woytekm/QSID/os/synth/lfo.c

#include "common.h"
#include "defs.h"
#include "patch.h"
#include "lfo.h"
#include "task.h"
#include "inventory.h"

void SYNTH_LFO1(void)
 {
  int LFO1_input_pipe;
  uint8_t retrigger, waveform_changed, routing_changed, input_msg, lfo_off, current_destination, i;
  int16_t LFO_step, mod_value, apply_value, apply_value_osc1,
           apply_value_osc2, apply_value_osc3, pipe_read_delay, falling_edge, readed;
  int16_t LFO_ranges[10];
  int16_t LFO_steps[10];

  lfo_off = 1;
  mod_value = 0;
  pipe_read_delay = 0;
  falling_edge = 1;

  apply_value = apply_value_osc1 = apply_value_osc2 = apply_value_osc3 = 0;

  LFO1_input_pipe = G_QSID_tasks[TASK_LFO1].input_pipe[0];

  if (fcntl(LFO1_input_pipe, F_SETFL, O_NONBLOCK) == -1) 
   {
    SYS_debug(DEBUG_NORMAL,"SYNTH_lfo1: fcntl on input pipe failed: %d", errno);
    return;
   }

  LFO_ranges[LFO_ROUTING_CUTOFF] = CUTOFF_RANGE;
  LFO_ranges[LFO_ROUTING_PW_1] = PW_RANGE;
  LFO_ranges[LFO_ROUTING_PW_2] = PW_RANGE;
  LFO_ranges[LFO_ROUTING_PW_3] = PW_RANGE;
  LFO_ranges[LFO_ROUTING_PW_ALL] = PW_RANGE;

  LFO_ranges[LFO_ROUTING_DETUNE_1] = DETUNE_RANGE;
  LFO_ranges[LFO_ROUTING_DETUNE_2] = DETUNE_RANGE;
  LFO_ranges[LFO_ROUTING_DETUNE_3] = DETUNE_RANGE;
  LFO_ranges[LFO_ROUTING_DETUNE_ALL] = DETUNE_RANGE;

  LFO_ranges[LFO_ROUTING_MAIN_VOLUME] = VOLUME_RANGE;

  LFO_steps[LFO_ROUTING_CUTOFF] = 20;
  LFO_steps[LFO_ROUTING_PW_1] = 50;
  LFO_steps[LFO_ROUTING_PW_2] = 50;
  LFO_steps[LFO_ROUTING_PW_3] = 50;
  LFO_steps[LFO_ROUTING_PW_ALL] = 50;

  LFO_steps[LFO_ROUTING_DETUNE_1] = 1;
  LFO_steps[LFO_ROUTING_DETUNE_2] = 1;
  LFO_steps[LFO_ROUTING_DETUNE_3] = 1;
  LFO_steps[LFO_ROUTING_DETUNE_ALL] = 1;

  LFO_steps[LFO_ROUTING_MAIN_VOLUME] = 1; 

  while( 1 )
   {

     usleep(LFO_BASE_TICK + (100000/G_current_patch.LFO1_rate));
     
     pipe_read_delay++;

     if(pipe_read_delay == 5)
      {
       readed = read(LFO1_input_pipe, &input_msg, sizeof(input_msg));
       pipe_read_delay = 0;
      }

     if(readed > 0)
      {
       SYS_debug(DEBUG_HIGH,"SYNTH_LFO1: input pipe data: 0x%X (readed %d bytes)",input_msg, readed);
       if((input_msg >= 0) && (input_msg <= 14))
        {
         if(input_msg == 0)
          {
           lfo_off = 1;
           //reset register values to patch settings here!
          }
         else if(input_msg <= 10)
          {
           routing_changed = 1;
           current_destination = input_msg;
           lfo_off = 0;
          }
         else 
           waveform_changed = 1;
        }
       readed = 0;
      }

     if(lfo_off) continue;

     if((waveform_changed) || (routing_changed))
      {
       mod_value = 0;
       LFO_step = LFO_steps[current_destination];
       waveform_changed = routing_changed = 0;
      }

     switch(G_current_patch.LFO1_shape)
      {
       case LFO_SHAPE_TRIANGLE:
        mod_value += LFO_step;
        /* printf("step: %d, mod value: %d\n",LFO_step, mod_value); */
        if((mod_value >= ((G_current_patch.LFO1_depth*LFO_steps[current_destination])/2)))
           {
            falling_edge = -1;
            LFO_step = LFO_steps[current_destination] * -1;
            /* printf("mod_value reached upper range, changing step to negative %d\n",LFO_step); */
           }
        else if((mod_value <= ((G_current_patch.LFO1_depth*LFO_steps[current_destination])/2) * -1 ))
           {
            falling_edge = 1;
            LFO_step = LFO_steps[current_destination];
            /* printf("mod_value reached lower range, changing step to positive %d\n",LFO_step); */
           }
        break;

       case LFO_SHAPE_SAWTOOTH:
        mod_value += LFO_step;
        if((mod_value >= (G_current_patch.LFO1_depth*LFO_step)/2))
          mod_value = ((G_current_patch.LFO1_depth*LFO_step)/2) * -1;
        break;
      }

    /* printf("LFO mod value: %d\n",mod_value); */
    /* printf("G_current_patch.LFO1_depth * falling_edge: %d\n",G_current_patch.LFO1_depth * falling_edge); */

    switch(current_destination)
     {
        case LFO_ROUTING_CUTOFF:
        apply_value = G_current_patch.filter_cutoff + mod_value + (G_current_patch.LFO1_depth * falling_edge);

        /* clip the value if it went out of range */
        if(apply_value < 0) apply_value = 0;
        else if(apply_value > LFO_ranges[current_destination]) 
         apply_value = LFO_ranges[current_destination];

        for(i = 1; i <= G_inventory_voice_count; i++)
          LIB_SID_modulate_cutoff(G_voice_inventory[i].address, apply_value);
        break;

        case LFO_ROUTING_PW_1:
        apply_value = G_current_patch.osc1_pw + mod_value;

        if(apply_value < 0) apply_value = 0;
        else if(apply_value > LFO_ranges[current_destination]) 
         apply_value = LFO_ranges[current_destination];

        for(i = 1; i <= G_inventory_voice_count; i++)
          LIB_SID_modulate_PW1(G_voice_inventory[i].address, apply_value);
        break;

        case LFO_ROUTING_PW_2:
        apply_value = G_current_patch.osc2_pw + mod_value;

        if(apply_value < 0) apply_value = 0;
        else if(apply_value > LFO_ranges[current_destination]) 
         apply_value = LFO_ranges[current_destination];

        for(i = 1; i <= G_inventory_voice_count; i++)
          LIB_SID_modulate_PW2(G_voice_inventory[i].address ,apply_value);
        break;

        case LFO_ROUTING_PW_3:
        apply_value = G_current_patch.osc3_pw + mod_value;

        if(apply_value < 0) apply_value = 0;
        else if(apply_value > LFO_ranges[current_destination]) 
         apply_value = LFO_ranges[current_destination];

        for(i = 1; i <= G_inventory_voice_count; i++)
          LIB_SID_modulate_PW3(G_voice_inventory[i].address ,apply_value);
        break;

        case LFO_ROUTING_PW_ALL:
        apply_value_osc1 = G_current_patch.osc1_pw + mod_value;
        apply_value_osc2 = G_current_patch.osc2_pw + mod_value;
        apply_value_osc3 = G_current_patch.osc3_pw + mod_value;

        if(apply_value_osc1 < 0) apply_value_osc1 = 0;
        else if(apply_value_osc1 > LFO_ranges[current_destination]) 
         apply_value_osc1 = LFO_ranges[current_destination];

        if(apply_value_osc2 < 0) apply_value_osc2 = 0;
        else if(apply_value_osc2 > LFO_ranges[current_destination])
         apply_value_osc2 = LFO_ranges[current_destination];

        if(apply_value_osc3 < 0) apply_value_osc3 = 0;
        else if(apply_value_osc3 > LFO_ranges[current_destination])
         apply_value_osc3 = LFO_ranges[current_destination];

        for(i = 1; i <= G_inventory_voice_count; i++)
         {
          LIB_SID_modulate_PW1(G_voice_inventory[i].address ,apply_value_osc1);
          LIB_SID_modulate_PW2(G_voice_inventory[i].address ,apply_value_osc2);
          LIB_SID_modulate_PW3(G_voice_inventory[i].address ,apply_value_osc3);
         }
        break;
     }

    /* printf("LFO apply value: %d\n",apply_value); */

   }

  }
