woytekm/QSID/os/midi/sysex_handlers.h

uint8_t MIDI_SYSEX_OSC1_STATE_CBK(unsigned char *message_buffer, uint16_t buffer_len);
uint8_t MIDI_SYSEX_OSC1_FINE_CBK(unsigned char *message_buffer, uint16_t buffer_len);
uint8_t MIDI_SYSEX_OSC1_COARSE_CBK(unsigned char *message_buffer, uint16_t buffer_len);
uint8_t MIDI_SYSEX_OSC1_PW_CBK(unsigned char *message_buffer, uint16_t buffer_len);
uint8_t MIDI_SYSEX_OSC1_WAVE_CBK(unsigned char *message_buffer, uint16_t buffer_len);
uint8_t MIDI_SYSEX_OSC1_RINGMOD_CBK(unsigned char *message_buffer, uint16_t buffer_len);
uint8_t MIDI_SYSEX_OSC1_SYNC_CBK(unsigned char *message_buffer, uint16_t buffer_len);
uint8_t MIDI_SYSEX_OSC1_ATTACK_CBK(unsigned char *message_buffer, uint16_t buffer_len);
uint8_t MIDI_SYSEX_OSC1_DECAY_CBK(unsigned char *message_buffer, uint16_t buffer_len);
uint8_t MIDI_SYSEX_OSC1_SUSTAIN_CBK(unsigned char *message_buffer, uint16_t buffer_len);
uint8_t MIDI_SYSEX_OSC1_RELEASE_CBK(unsigned char *message_buffer, uint16_t buffer_len);
uint8_t MIDI_SYSEX_OSC1_FILTER_CBK(unsigned char *message_buffer, uint16_t buffer_len);
uint8_t MIDI_SYSEX_OSC2_STATE_CBK(unsigned char *message_buffer, uint16_t buffer_len);
uint8_t MIDI_SYSEX_OSC2_FINE_CBK(unsigned char *message_buffer, uint16_t buffer_len);
uint8_t MIDI_SYSEX_OSC2_COARSE_CBK(unsigned char *message_buffer, uint16_t buffer_len);
uint8_t MIDI_SYSEX_OSC2_PW_CBK(unsigned char *message_buffer, uint16_t buffer_len);
uint8_t MIDI_SYSEX_OSC2_WAVE_CBK(unsigned char *message_buffer, uint16_t buffer_len);
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
uint8_t MIDI_SYSEX_TRANSMT_PATCH_DTA_CBK(unsigned char *message_buffer, uint16_t buffer_len);
uint8_t MIDI_SYSEX_RECV_BANK_CBK(unsigned char *message_buffer, uint16_t buffer_len);
uint8_t MIDI_SYSEX_RECV_PATCH_CBK(unsigned char *message_buffer, uint16_t buffer_len);
