woytekm/QSID/os/synth/voice.h

/*
 Q-SID OS

 polyphony manager data structures
*/


/* alternate voice allocation directions */
#define LEFT_TO_RIGHT 1
#define RIGHT_TO_LEFT 0

uint8_t G_voice_allocation_dir;
uint8_t G_playing_voices;
