woytekm/QSID/os/system/task.h

/*
 thread (task) array for QSID OS
*/

#define QSID_OS_MAX_TASK 127
#define QSID_OS_MAX_TASK_NAME_LEN 128

#define PRIO_VERYHIGH99 99
#define PRIO_VERYHIGH98 98
#define PRIO_VERYHIGH97 97
#define PRIO_VERYHIGH96 96
#define PRIO_VERYHIGH95 95
#define PRIO_VERYHIGH94 94
#define PRIO_VERYHIGH93 93
#define PRIO_VERYHIGH92 92
#define PRIO_VERYHIGH91 91
#define PRIO_VERYHIGH90 90

#define PRIO_HIGH89 89
#define PRIO_HIGH88 88
#define PRIO_HIGH87 87
#define PRIO_HIGH86 86
#define PRIO_HIGH85 85
#define PRIO_HIGH84 84
#define PRIO_HIGH83 83
#define PRIO_HIGH82 82
#define PRIO_HIGH81 81
#define PRIO_HIGH80 80

#define PRIO_NORMAL59 59
#define PRIO_NORMAL58 58
#define PRIO_NORMAL57 57
#define PRIO_NORMAL56 56
#define PRIO_NORMAL55 55
#define PRIO_NORMAL54 54
#define PRIO_NORMAL53 53
#define PRIO_NORMAL52 52
#define PRIO_NORMAL51 51
#define PRIO_NORMAL50 50

#define PRIO_LOW29 29
#define PRIO_LOW28 28
#define PRIO_LOW27 27
#define PRIO_LOW26 26
#define PRIO_LOW25 25
#define PRIO_LOW24 24
#define PRIO_LOW23 23
#define PRIO_LOW22 22
#define PRIO_LOW21 21
#define PRIO_LOW20 20

#define TASK_MIDI_IN 1
#define TASK_SID_WRITER 2
#define TASK_UDP_MIDI_IN 3

#define TASK_LFO1   64
#define TASK_LFO2   65

#define TASK_LFO1V1 64
#define TASK_LFO2V1 65
#define TASK_LFO1V2 66
#define TASK_LFO2V2 67
#define TASK_LFO1V3 68
#define TASK_LFO2V3 69
#define TASK_LFO1V4 70
#define TASK_LFO2V4 71
#define TASK_LFO1V5 72
#define TASK_LFO2V5 73
#define TASK_LFO1V6 74
#define TASK_LFO2V6 75
#define TASK_LFO1V7 76
#define TASK_LFO2V7 77
#define TASK_LFO1V8 78
#define TASK_LFO2V8 79

#define TASK_HARDWARE_INPUT 4

#define TASK_FILTER_ADSR_V1 5
#define TASK_FILTER_ADSR_V2 6
#define TASK_FILTER_ADSR_V3 7
#define TASK_FILTER_ADSR_V4 8
#define TASK_FILTER_ADSR_V5 9
#define TASK_FILTER_ADSR_V6 10
#define TASK_FILTER_ADSR_V7 11
#define TASK_FILTER_ADSR_V8 12


#define TASK_SILENCER_V1O1 17
#define TASK_SILENCER_V1O2 33
#define TASK_SILENCER_V1O3 49

#define TASK_SILENCER_V2O1 18
#define TASK_SILENCER_V2O2 34
#define TASK_SILENCER_V2O3 50

#define TASK_SILENCER_V3O1 19
#define TASK_SILENCER_V3O2 35
#define TASK_SILENCER_V3O3 51

#define TASK_SILENCER_V4O1 20
#define TASK_SILENCER_V4O2 36
#define TASK_SILENCER_V4O3 52

#define TASK_SILENCER_V5O1 21
#define TASK_SILENCER_V5O2 37
#define TASK_SILENCER_V5O3 53

#define TASK_SILENCER_V6O1 22
#define TASK_SILENCER_V6O2 38
#define TASK_SILENCER_V6O3 54

#define TASK_SILENCER_V7O1 23
#define TASK_SILENCER_V7O2 39
#define TASK_SILENCER_V7O3 55

#define TASK_SILENCER_V8O1 24
#define TASK_SILENCER_V8O2 40
#define TASK_SILENCER_V8O3 56


typedef struct _QSID_task_t {
  pthread_t task_id;
  int input_pipe[2];
 } QSID_task_t;

QSID_task_t G_QSID_tasks[QSID_OS_MAX_TASK];

uint8_t G_QSID_task_count;
