woytekm/QSID/player/sidplay-libs-2.1.1/builders/hardsid-builder/src/MCP23017.h

//
// Q-SID OS MCP23017 (voice board control) defines
//
//

#define MCP23017_GPIO_OUT 0
#define MCP23017_GPIO_IN  1
#define MCP23017_FIRSTADDR 0x20
#define MCP23017_LASTADDR 0x27

#define MCP23017_IODIR_A 0x0
#define MCP23017_IODIR_B 0x1

#define MCP23017_GPPU_A 0x0C
#define MCP23017_GPPU_B 0x0D
#define MCP23017_GPIO_A 0x12
#define MCP23017_GPIO_B 0x13
#define MCP23017_OLAT_A 0x14
#define MCP23017_OLAT_B 0x15
